charutomo/Plan-Bee-/for ESP32/for SH1106/SH1106/SH1106.ino

#include <SPI.h>
#include <Wire.h>
#include <Beastdevices_INA3221.h>
#include <Adafruit_GFX.h>
#include <Adafruit_SH1106.h>
#include <DallasTemperature.h>


#define OLED_SDA 21
#define OLED_SCL 22

Adafruit_SH1106 display(21, 22);

#define LOGO_HEIGHT 64 
#define LOGO_WIDTH  128 

#define PRINT_DEC_POINTS  3   

#define SENSOR_PIN  21 // ESP32 pin GPIO21 connected to DS18B20 sensor's DQ pin
#define BUTTON_PIN 4 // GPIO4 pin connected to button

Beastdevices_INA3221 ina3221(INA3221_ADDR40_GND);

OneWire oneWire(SENSOR_PIN);
DallasTemperature DS18B20(&oneWire);

float tempC; // temperature in Celsius
float tempF; // temperature in Fahrenheit
int clicknum;
int lastState = HIGH;
int currentState;    

static const unsigned char PROGMEM logo_bmp[] =
  {0xff, 0xff, 0xff, 0xff, 0xff, 0xff, 0xff, 0xff, 0xff, 0xff, 0xff, 0xff, 0xff, 0xff, 0xff, 0xff, 
 0xff, 0xff, 0xff, 0xff, 0xff, 0xff, 0xff, 0xff, 0xff, 0xff, 0xff, 0xff, 0xff, 0xff, 0xff, 0xff, 
  0xff, 0xff, 0xff, 0xff, 0xff, 0xff, 0xff, 0xff, 0xff, 0xff, 0xff, 0xff, 0xff, 0xff, 0xff, 0xff, 
  0xff, 0xff, 0xff, 0xff, 0xff, 0xff, 0xff, 0xff, 0xff, 0xff, 0xff, 0xff, 0xff, 0xff, 0xff, 0xff, 
  0xff, 0xff, 0xff, 0xff, 0xff, 0xff, 0xff, 0xff, 0xff, 0xff, 0xff, 0xff, 0xff, 0xff, 0xff, 0xff, 
  0xff, 0xff, 0xff, 0xff, 0xff, 0xff, 0xff, 0xff, 0xf8, 0x07, 0xff, 0xff, 0xff, 0xff, 0xff, 0xff, 
  0xff, 0xff, 0xff, 0xff, 0xff, 0xff, 0xff, 0xff, 0x8f, 0xfe, 0x3f, 0xff, 0xff, 0xff, 0xff, 0xff, 
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
  0xff, 0xff, 0xff, 0xf7, 0xff, 0xfe, 0x07, 0xef, 0xfe, 0x00, 0x7f, 0xe7, 0x8f, 0xff, 0xfb, 0xff, 
  0xff, 0xff, 0xff, 0xf9, 0xff, 0xf8, 0x0f, 0x9f, 0xf8, 0x04, 0x3f, 0xf9, 0x3f, 0xff, 0xfb, 0xff, 
  0xff, 0xff, 0xff, 0xfe, 0xff, 0xf8, 0x3f, 0x3f, 0xe0, 0x1f, 0x9f, 0xfc, 0xff, 0xff, 0xfb, 0xff, 
  0xff, 0xff, 0xff, 0xff, 0x3f, 0xf8, 0x7e, 0x3f, 0xc0, 0x7f, 0xbf, 0xff, 0x3f, 0xff, 0xf7, 0xff, 
  0xff, 0xff, 0xff, 0xff, 0xdf, 0xf8, 0xfe, 0x3e, 0x00, 0xff, 0x3f, 0x9f, 0xdf, 0xff, 0xef, 0xff, 
  0xff, 0xff, 0xff, 0xff, 0xf7, 0xfc, 0x3f, 0x9c, 0x03, 0xdf, 0x7e, 0x03, 0xe7, 0xff, 0x9f, 0xff, 
  0xff, 0xff, 0xff, 0xff, 0xf9, 0xff, 0xcf, 0xc0, 0x0f, 0x3e, 0xfc, 0x01, 0xf3, 0xfe, 0x7f, 0xff, 
  0xff, 0xff, 0xff, 0xff, 0xfe, 0x7f, 0xf1, 0x20, 0x38, 0x7d, 0xf8, 0x18, 0xcc, 0x03, 0xff, 0xff, 
  0xff, 0xff, 0xff, 0xff, 0xff, 0x9f, 0xfe, 0xe0, 0xf0, 0xf9, 0xf0, 0x3e, 0x02, 0x7f, 0xff, 0xff, 
  0xff, 0xff, 0xff, 0xff, 0xff, 0xe7, 0xff, 0xe3, 0xf8, 0xfb, 0xc0, 0xfe, 0x00, 0x3f, 0xff, 0xff, 
  0xff, 0xff, 0xff, 0xff, 0xff, 0xfc, 0xff, 0xf3, 0x07, 0xf7, 0x81, 0xfe, 0x00, 0x1f, 0xff, 0xff, 
  0xff, 0xff, 0xff, 0xff, 0xff, 0xff, 0x3f, 0xfe, 0x43, 0xe7, 0x07, 0xfe, 0x1e, 0x4f, 0xff, 0xff, 
  0xff, 0xff, 0xff, 0xff, 0xff, 0xff, 0xcf, 0xff, 0xe3, 0xce, 0x0f, 0xfc, 0x7e, 0xe7, 0xff, 0xff, 
  0xff, 0xff, 0xff, 0xff, 0xff, 0xff, 0xf9, 0xff, 0xf3, 0xd8, 0x1f, 0xfc, 0xf9, 0xf7, 0xff, 0xff, 
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


void setup() {
  Serial.begin(115200);
  DS18B20.begin();
  pinMode(BUTTON_PIN, INPUT);
  display.begin(SH1106_SWITCHCAPVCC, 0x3C);
  for (int i = 1; i <= 4; ++i) {
        testdrawbitmap();
        }

   // Draw a small bitmap image
  ina3221.begin();
  ina3221.reset();
  ina3221.setShuntRes(100, 100, 100);
}

void loop() {
  currentState = digitalRead(BUTTON_PIN);
  Serial.print(currentState);
  int index = clicknum%4;
  switch(index){
    case 0:
      showbatt();
      ifClick();
      break;
    case 1:
      temperature();
      ifClick();
      break;
    case 2:
      textdisplay();
      ifClick();
      break;
    case 3:
      tech(); 
      ifClick();
      break;
  }
  /*if(clicknum%4==0){
    showbatt();
  }
  else if (clicknum%4==1){
    temperature();
  }
  else if (clicknum%4==2){
    thanks();
  }
  else{
    tech();
  }*/

  lastState = currentState;
}

void lowbatt(void){
  display.clearDisplay();
  display.drawBitmap(
  (display.width()  - LOGO_WIDTH ) / 2,
  (display.height() - LOGO_HEIGHT) / 2,
  logodead_bmp, LOGO_WIDTH, LOGO_HEIGHT, 1);
  display.display();
  delay(500);
  display.clearDisplay();
  display.display();
  delay(500);
}


void testdrawbitmap(void) {
  display.clearDisplay();

  display.drawBitmap(
    (display.width()  - LOGO_WIDTH ) / 2,
    (display.height() - LOGO_HEIGHT) / 2,
    logo_bmp, LOGO_WIDTH, LOGO_HEIGHT, 1);
  display.display();
  delay(200);
  display.clearDisplay();

  display.drawBitmap(
    (display.width()  - LOGO_WIDTH ) / 2,
    (display.height() - LOGO_HEIGHT) / 2,
    logo2_bmp, LOGO_WIDTH, LOGO_HEIGHT, 1);
  display.display();
  delay(500);
  display.clearDisplay();
}


void textdisplay(void){
    display.clearDisplay();
    display.setTextSize(2);
    display.setTextColor(WHITE);
    display.setCursor(0, 0);
    display.println("Plan Bee");
//  display.println("Group");
//  display.println("Members:");
//  display.display();
//  delay(1000);
//  
//  display.clearDisplay();
//  display.setTextSize(2);
//  display.setTextColor(WHITE);
//  display.setCursor(0, 0);
//  display.println("Andy, ");
//  display.println("Jia Woei,");
//  display.println("Jinghui, ");
//  display.display();
//  delay(1000);
//  
//  display.clearDisplay();
//  display.setTextSize(2);
//  display.setTextColor(WHITE);
//  display.setCursor(0, 0);
//  display.println("Charissa");
//  display.println("and");
//  display.println("Chermaine");
//  display.display();
//  delay(1000);
//  
//  
//  display.clearDisplay();
//  display.setTextSize(2);
//  display.setTextColor(WHITE);
//  display.setCursor(0, 0);
  display.println("Thanks to");
  display.println("Tony and");
  display.println("Qi Jie");
  display.display();
  delay(1000);
  
}


void thanks(void){
  display.clearDisplay();
  display.setTextSize(2);
  display.setTextColor(WHITE);
  display.setCursor(0, 0);
  display.println("Thank You");
  display.println("Have a");
  display.println("Nice Day:)");
  display.display();
  delay(1000);
  }

void temperature(void){
  DS18B20.requestTemperatures();       // send the command to get temperatures
  tempC = DS18B20.getTempCByIndex(0);  // read temperature in °C
  tempF = tempC * 9 / 5 + 32;
  display.clearDisplay();
  display.setTextSize(2);
  display.setTextColor(WHITE);
  display.setCursor(0, 0);
  display.println("Temp:");
  display.print(tempC);
  display.println("°C");
  display.print(tempF);
  display.println("°F");
  display.display();
  delay(1000);
}

void showbatt(void){
  float current[3];
  float voltage[3];
  current[0] = ina3221.getCurrent(INA3221_CH1);
  voltage[0] = ina3221.getVoltage(INA3221_CH1);
  float power1 = current[0] * voltage[0];
  float battpercent = ((voltage[0]-3.4)/(4.3-3.4))*100;

  current[1] = ina3221.getCurrent(INA3221_CH2);
  voltage[1] = ina3221.getVoltage(INA3221_CH2);
  float power2 = current[1] * voltage[1];

  current[2] = ina3221.getCurrent(INA3221_CH3);
  voltage[2] = ina3221.getVoltage(INA3221_CH3);
  float power3 = current[2] * voltage[2];

  display.clearDisplay();
  display.setTextSize(2);
  display.setTextColor(WHITE);
  display.setCursor(0, 0);
  display.println("At Batt:");
  display.print(current[0], PRINT_DEC_POINTS);
  display.println("A, ");
  display.print(voltage[0], PRINT_DEC_POINTS);
  display.println("V, ");
  display.print(power1);
  display.println("W");
  display.display();
  delay(500);
  
  if (battpercent<0) {
    display.clearDisplay();
    display.setTextColor(WHITE);
    display.setCursor(0, 0);
    display.println("Please");
    display.println("Connect");
    display.println("To ");
    display.print("Battery.");
    display.display();
    delay(1000);
   } 
   
   else if(battpercent<=10){
      for (int i = 1; i <= 6; ++i) {
        lowbatt();
         }
      display.clearDisplay();
      display.setTextColor(WHITE);
      display.setCursor(0, 0);
      display.println("Battery");
      display.println("Percent:");
      display.print(battpercent);
      display.println("%");
      display.display();
      delay(1000);

   }

   else{
    display.clearDisplay();
    display.setTextSize(2);
    display.setTextColor(WHITE);
    display.setCursor(0, 0);
    display.print("Battery");
    display.print("Percent:");
    display.print(battpercent);
    display.print("%");
    display.display();
    delay(1000);
   }
   
  /*
  display.clearDisplay();
  display.setTextSize(2);
  display.setTextColor(WHITE);
  display.setCursor(0, 0);
  display.println("B4 Batt:");
  display.print(current[1], PRINT_DEC_POINTS);
  display.println("A, ");
  display.print(voltage[1], PRINT_DEC_POINTS);
  display.println("V, ");
  display.print(power2);
  display.println("W");
  display.display();
  delay(1000);

  display.clearDisplay();
  display.setTextSize(2);
  display.setTextColor(WHITE);
  display.setCursor(0, 0);
  display.println("Aft FWR:");
  display.print(current[2], PRINT_DEC_POINTS);
  display.println("A, ");
  display.print(voltage[2], PRINT_DEC_POINTS);
  display.println("V, ");
  display.print(power3);
  display.println("W");
  display.display();
  delay(1000);
  */
}

void tech(void){
  display.clearDisplay();
  display.setTextSize(2);
  display.setTextColor(WHITE);
  display.setCursor(0, 0);
  display.println("Contact us");
  display.println("at planbee9555@gmail.com");
  display.display();
}

void ifClick(void){
    if (lastState == LOW && currentState == HIGH){
    clicknum++;
  }
}
