charutomo/Plan-Bee-/for ESP32/for ILI9341/ILI9341_INA3221/samplingtest/samplingtest.ino

#include "SPI.h"
#include "Adafruit_ILI9341.h"
#include <Wire.h>
#include <Beastdevices_INA3221.h>

#define TFT_CLK 32
#define TFT_MOSI 33
#define TFT_MISO 12
#define TFT_CS 27
#define TFT_DC 26
#define TFT_RST 25

#define SERIAL_SPEED      115200    // serial baud rate
#define PRINT_DEC_POINTS  3         // decimal points to print

// Set I2C address to 0x41 (A0 pin -> VCC)
Beastdevices_INA3221 ina3221(INA3221_ADDR40_GND);

Adafruit_ILI9341 tft = Adafruit_ILI9341(TFT_CS, TFT_DC, TFT_MOSI, TFT_CLK, TFT_RST, TFT_MISO);

float currentarray1[50];
float voltagearray1[50];
float powerarray1[50];
int numloop = 0;

void setup() {
  Serial.begin(SERIAL_SPEED);

  while (!Serial) {
      delay(1);
  }
  tft.begin();
  tft.fillScreen(ILI9341_WHITE);
  ina3221.begin();
  ina3221.reset();

  // Set shunt resistors to 10 mOhm for all channels
  ina3221.setShuntRes(100, 100, 100);
}

void loop() {
  if (numloop<50){
  float current[3];
  float voltage[3];

  Serial.println(numloop);
  current[0] = ina3221.getCurrent(INA3221_CH1);
  currentarray1[numloop] = ina3221.getCurrent(INA3221_CH1);
  voltage[0] = ina3221.getVoltage(INA3221_CH1);
  voltagearray1[numloop] = ina3221.getVoltage(INA3221_CH1);

  /*current[1] = ina3221.getCurrent(INA3221_CH2);
  voltage[1] = ina3221.getVoltage(INA3221_CH2);

  current[2] = ina3221.getCurrent(INA3221_CH3);
  voltage[2] = ina3221.getVoltage(INA3221_CH3);*/

  Serial.print("Channel 1: ");
  Serial.print(current[0], PRINT_DEC_POINTS);
  Serial.print("A, ");
  Serial.print(voltage[0], PRINT_DEC_POINTS);
  Serial.println("V");
  Serial.println();

  /*Serial.print("Channel 2: ");
  Serial.print(current[1], PRINT_DEC_POINTS);
  Serial.print("A, ");
  Serial.print(voltage[1], PRINT_DEC_POINTS);
  Serial.println("V");

  Serial.print("Channel 3: ");
  Serial.print(current[2], PRINT_DEC_POINTS);
  Serial.print("A, ");
  Serial.print(voltage[2], PRINT_DEC_POINTS);
  Serial.println("V");
  Serial.println();*/

  Serial.print("Current Array:");
  for (int i = 0; i < 50; i = i + 1) {
    Serial.print(currentarray1[i]);
    Serial.print(", ");
  }
  
  Serial.println();
  Serial.print("Voltage Array:");
  for (int i = 0; i < 50; i = i + 1) {
    Serial.print(voltagearray1[i]);
    Serial.print(", ");
  }
  Serial.println();
  numloop+=1;
  delay(5);
  }
  else if(numloop == 50){
    tft.fillScreen(ILI9341_WHITE);
    tft.setRotation(0);
    tft.setCursor(40,40);
    tft.setTextSize(2);
    tft.setTextColor(ILI9341_BLACK);
    Serial.print("Current:");
    Serial.println(avgvalue(currentarray1,numloop));
    tft.print("Current:");
    tft.print(avgvalue(currentarray1,numloop));
    tft.println("A");
    tft.setCursor(40,70);
    Serial.print("Voltage:");
    Serial.println(avgvalue(voltagearray1,numloop));
    tft.print("Voltage:");
    tft.print(avgvalue(voltagearray1,numloop));
    tft.println("V");
    tft.setCursor(40,100);
    Serial.print("Power:");
    Serial.println(avgvalue(powerarr(currentarray1,voltagearray1),numloop));
    tft.print("Power:");
    tft.print(avgvalue(powerarr(currentarray1,voltagearray1),numloop));
    tft.println("W");
    tft.setCursor(40,130);
    Serial.print("Energy:");
    Serial.println(energy(powerarr(currentarray1,voltagearray1)));
    tft.print("Energy:");
    tft.print(energy(powerarr(currentarray1,voltagearray1)));
    tft.println("Ws");
    numloop=0;
    for (int i=0; i<50; i++){
      currentarray1[i]=0;
      voltagearray1[i]=0;
    delay(100);
    Serial.println("New Loop");
  }
  
  }
  
}

float avgvalue(float arr1[50], int numloop){
    float totalval = 0;
    for (int i = 0; i < numloop; i++){
      totalval += arr1[i];
    }
    float avgval = totalval/numloop;
    return avgval;
}

float* powerarr(float carr1[50], float varr[50]){
  for (int i = 0; i <50; i++){
    powerarray1[i] = carr1[i]*varr[i];
  }
  return powerarray1;
}


float energy(float powerarr[50]){
  float avgenergy = 0;
  for (int i = 0; i <50; i++){
    avgenergy+= powerarr[i]*0.005;
  }
  return avgenergy;
}
